ManojBR105/Soldering-Station/EAGLE FILES/Soldering Station/Board.png

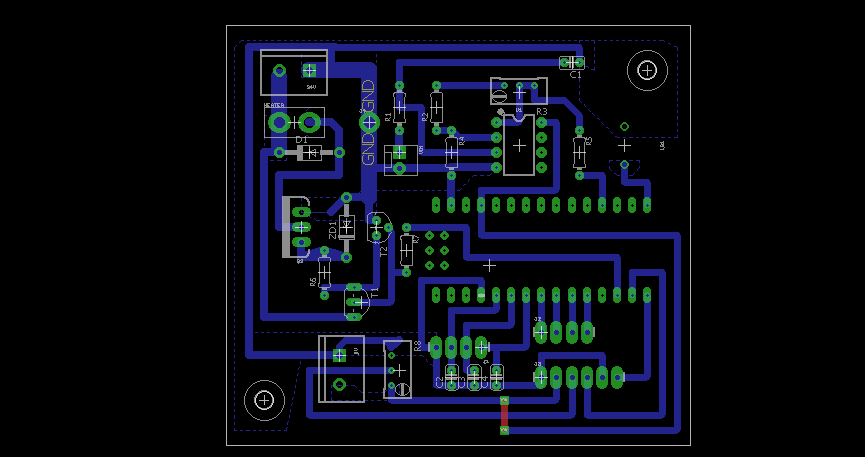
EAGLE FILES/Soldering Station/Board.png
